mlundh/BLEtarget/fw/BleTarget/App/src/app.c

#include "app.h"
#include "sensor.h"
#include "i2c_slave.h"
#include "serialization.h"
#include "i2c_master.h"
#include "slip_packet.h"

#define MESSAGE_SIZE (5*4)

static uint8_t master = 1;
static SLIP_t *slipPacket = NULL;
static UART_HandleTypeDef *uartInstance = NULL;
static TIM_TypeDef *timer = TIM17; // 2s timer used to transmit heartbeat.
static uint8_t newHeartbeat = 0;
typedef enum{
  hitData = 0,
  heartbeat = 1
}messageId_t;


void invalidateData();

void app_init(I2C_HandleTypeDef* hi2c, UART_HandleTypeDef* huart)
{
  uartInstance = huart;
  slipPacket = Slip_Create(32);
  master = (GPIO_PIN_RESET == HAL_GPIO_ReadPin(BOOT_GPIO_Port,BOOT_Pin));



  if(master)
  {
    I2C_master_init(hi2c);
    Sensor_init(master, NULL); // do not need to invalidate data as the master.

    // Start the heartbeat timer.
    LL_TIM_SetCounter(timer, 0);
    LL_TIM_ClearFlag_UPDATE(timer);
    LL_TIM_EnableIT_UPDATE(timer);
    LL_TIM_EnableCounter(timer);
  }
  else
  {
    I2C_slave_init(hi2c);
    Sensor_init(master, &invalidateData); // Data will be invalidated after the lockout period.
  }
}

void taskCyclic()
{
  if(newHeartbeat)
  {
    newHeartbeat = 0;
    sendHeartbeat();
  }
  if(Sensor_newValue())
  {
    int32_t position = Sensor_getPos();
    float speedF = Sensor_getSpeed();
    Sensor_clear();

    int32_t speed = (int32_t)speedF;
    //int32_t speedDecimal = (int32_t)((speedF - speed) * 1000); // to use if more resoultion is needed...


    if(master)
    {

      // Read data from slave.
      uint8_t buffer[DATA_LENGTH];
      uint8_t *bufferP = buffer;
      uint32_t bufferSize = DATA_LENGTH;
      int32_t positionY = ERROR;
      int32_t speedY = SPEED_ERROR;

      positionY = 0;
      speedY = 0;

      if(I2C_master_read(buffer, DATA_LENGTH))
      {
        bufferP = deserialize_int32_t(bufferP, &bufferSize, &positionY);
        bufferP = deserialize_int32_t(bufferP, &bufferSize, &speedY);
      }

      // Transmit data, serial over USB
      uint8_t message[MESSAGE_SIZE];
      uint8_t *messageP = message;
      uint32_t messageSize = MESSAGE_SIZE;
      int32_t messageId = hitData;

      messageP = serialize_int32_t(messageP, &messageSize, &messageId);
      messageP = serialize_int32_t(messageP, &messageSize, &position);
      messageP = serialize_int32_t(messageP, &messageSize, &positionY);
      messageP = serialize_int32_t(messageP, &messageSize, &speed);
      messageP = serialize_int32_t(messageP, &messageSize, &speedY);

      Slip_Packetize(message, MESSAGE_SIZE, slipPacket);

      CDC_Transmit_FS(slipPacket->payload, slipPacket->packetSize);
      HAL_UART_Transmit(uartInstance, slipPacket->payload, slipPacket->packetSize, 1000);
    }
    else
    {
      uint8_t buffer[DATA_LENGTH];
      uint8_t *bufferP = buffer;
      uint32_t bufferSize = DATA_LENGTH;

      bufferP = serialize_int32_t(bufferP, &bufferSize, &position);
      bufferP = serialize_int32_t(bufferP, &bufferSize, &speed);

      I2C_slave_updateData(buffer);
    }
    //LOG_ENTRY("Position: %d, Speed: %d,%d", (int)position, (int)speedInt, (int)speedDecimal);


  }

}

void invalidateData()
{
  uint8_t buffer[DATA_LENGTH] = {0};
  uint8_t *bufferP = buffer;
  uint32_t bufferSize = DATA_LENGTH;

  int32_t position = ERROR;
  int32_t speed = SPEED_ERROR;

  bufferP = serialize_int32_t(bufferP, &bufferSize, &position);
  bufferP = serialize_int32_t(bufferP, &bufferSize, &speed);

  I2C_slave_updateData(buffer);
}

void sendHeartbeat()
{
  // Transmit data, serial over USB
  uint8_t message[MESSAGE_SIZE];
  uint8_t *messageP = message;
  uint32_t messageSize = MESSAGE_SIZE;
  int32_t messageId = heartbeat;
  int32_t zero = 0;

  messageP = serialize_int32_t(messageP, &messageSize, &messageId);
  messageP = serialize_int32_t(messageP, &messageSize, &zero);
  messageP = serialize_int32_t(messageP, &messageSize, &zero);
  messageP = serialize_int32_t(messageP, &messageSize, &zero);
  messageP = serialize_int32_t(messageP, &messageSize, &zero);

  Slip_Packetize(message, MESSAGE_SIZE, slipPacket);

  CDC_Transmit_FS(slipPacket->payload, slipPacket->packetSize);
  HAL_UART_Transmit(uartInstance, slipPacket->payload, slipPacket->packetSize, 1000);
}

void timer17UpdateISR()
{
  LL_TIM_ClearFlag_UPDATE(timer);
  newHeartbeat = 1;
}
