mlundh/BLEtarget/fw/BleTarget/App/src/serialization.c

/*
 * serialization.c
 *
 * Copyright (C) 2017 Martin Lundh
 *
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
 * THE SOFTWARE IS PROVIDED "AS IS", WITHOUT WARRANTY OF ANY KIND, EXPRESS OR
 * IMPLIED, INCLUDING BUT NOT LIMITED TO THE WARRANTIES OF MERCHANTABILITY,
 * FITNESS FOR A PARTICULAR PURPOSE AND NONINFRINGEMENT. IN NO EVENT SHALL THE
 * AUTHORS OR COPYRIGHT HOLDERS BE LIABLE FOR ANY CLAIM, DAMAGES OR OTHER
 * LIABILITY, WHETHER IN AN ACTION OF CONTRACT, TORT OR OTHERWISE, ARISING FROM,
 * OUT OF OR IN CONNECTION WITH THE SOFTWARE OR THE USE OR OTHER DEALINGS IN
 * THE SOFTWARE.
 */
#include "serialization.h"
#include <string.h>
uint8_t* serialize_uint32_t(uint8_t *buffer, uint32_t* size, uint32_t* value)
{
    if(!buffer || *size < 4)
    {
        return 0;
    }
    buffer[0]  = (uint8_t)((*value >> 24)   & 0xFF);
    buffer[1]  = (uint8_t)((*value >> 16)   & 0xFF);
    buffer[2]  = (uint8_t)((*value >> 8)    & 0xFF);
    buffer[3]  = (uint8_t)((*value)         & 0xFF);
    *size -= 4;
    return buffer + 4;
}

uint8_t* deserialize_uint32_t(uint8_t *buffer, uint32_t* size, uint32_t* value)
{
    if(!buffer || *size < 4)
    {
        return 0;
    }
    *value = (((int32_t)buffer[0]) << 24)+
            (((int32_t)buffer[1]) << 16) +
            (((int32_t)buffer[2]) << 8) +
            ((int32_t)buffer[3]);
    ;
    *size -= 4;
    return buffer + 4;
}

uint8_t* serialize_int32_t(uint8_t *buffer, uint32_t* size, int32_t *value)
{
    return serialize_uint32_t(buffer, size, (uint32_t*)value);
}

uint8_t* deserialize_int32_t(uint8_t *buffer, uint32_t* size, int32_t* value)
{
    return deserialize_uint32_t(buffer, size, (uint32_t*)value);
}

uint8_t* serialize_uint16_t(uint8_t *buffer, uint32_t* size, uint16_t* value)
{
    if(!buffer || *size < 2)
    {
        return 0;
    }
    buffer[0]  = (uint8_t)((*value >> 8)    & 0xFF);
    buffer[1]  = (uint8_t)((*value)         & 0xFF);
    *size -= 2;
    return buffer + 2;
}

uint8_t* deserialize_uint16_t(uint8_t *buffer, uint32_t* size, uint16_t* value)
{
    if(!buffer || *size < 2)
    {
        return 0;
    }
    *value = (((int32_t)buffer[0]) << 8) +
              ((int32_t)buffer[1]);
    ;
    *size -= 2;
    return buffer + 2;
}

uint8_t* serialize_int16_t(uint8_t *buffer, uint32_t* size, int16_t *value)
{
    return serialize_uint16_t(buffer, size, (uint16_t*)value);
}

uint8_t* deserialize_int16_t(uint8_t *buffer, uint32_t* size, int16_t* value)
{
    return deserialize_uint16_t(buffer, size, (uint16_t*)value);
}


uint8_t* serialize_int8_t(uint8_t *buffer, uint32_t* size, int8_t *value)
{
    return serialize_uint8_t(buffer, size, (uint8_t*)value);
}

uint8_t* deserialize_int8_t(uint8_t *buffer, uint32_t* size, int8_t* value)
{
    return deserialize_uint8_t(buffer, size, (uint8_t*)value);
}

uint8_t* serialize_uint8_t(uint8_t *buffer, uint32_t* size, uint8_t *value)
{
    if(!buffer || *size < 4)
    {
        return 0;
    }
    buffer[0]  = (uint8_t)*value;
    *size-=1;
    return buffer + 1;
}

uint8_t* deserialize_uint8_t(uint8_t *buffer, uint32_t* size, uint8_t* value)
{
    if(!buffer || *size < 1)
    {
        return 0;
    }
    *value = ((int8_t)buffer[0]);
    *size -= 1;
    return buffer + 1;
}
